nnandrew/heartbreak/CONCEPTS/backPCB.png

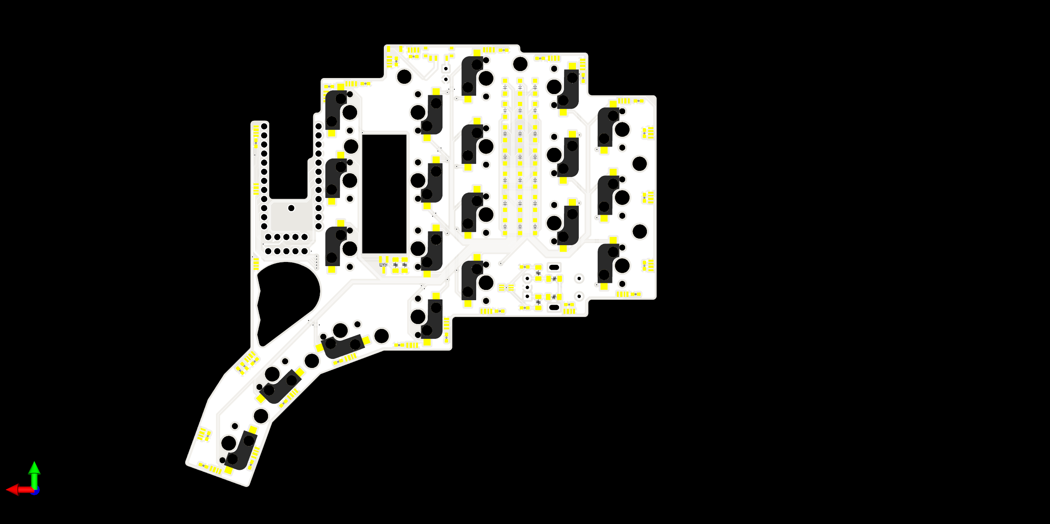
CONCEPTS/backPCB.png
