nnandrew/heartbreak/CONCEPTS/centerGlow.png

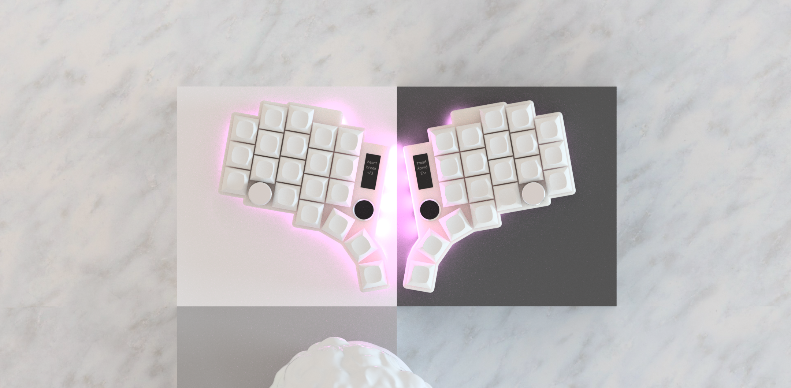
CONCEPTS/centerGlow.png
