nnandrew/heartbreak/CONCEPTS/david.png

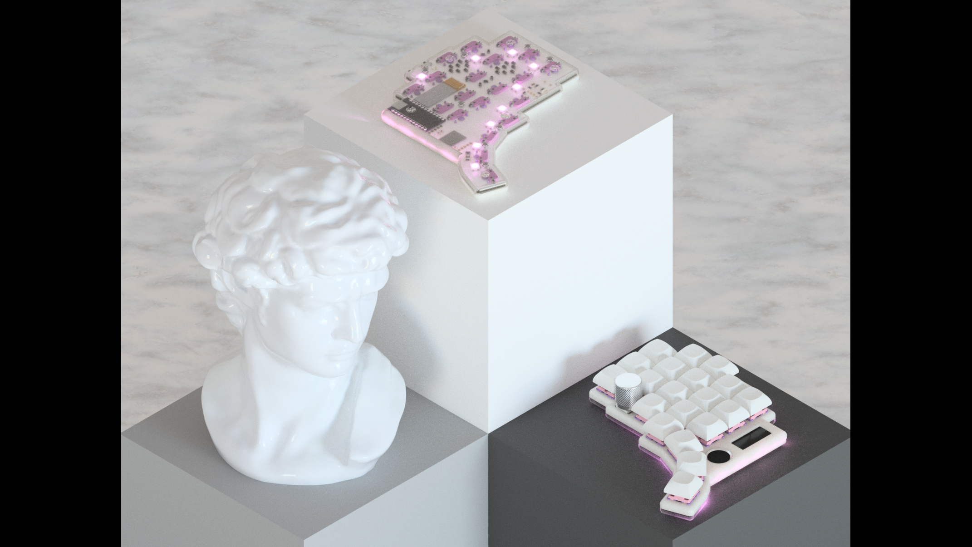
CONCEPTS/david.png
