nnandrew/heartbreak/CONCEPTS/davidraw.png

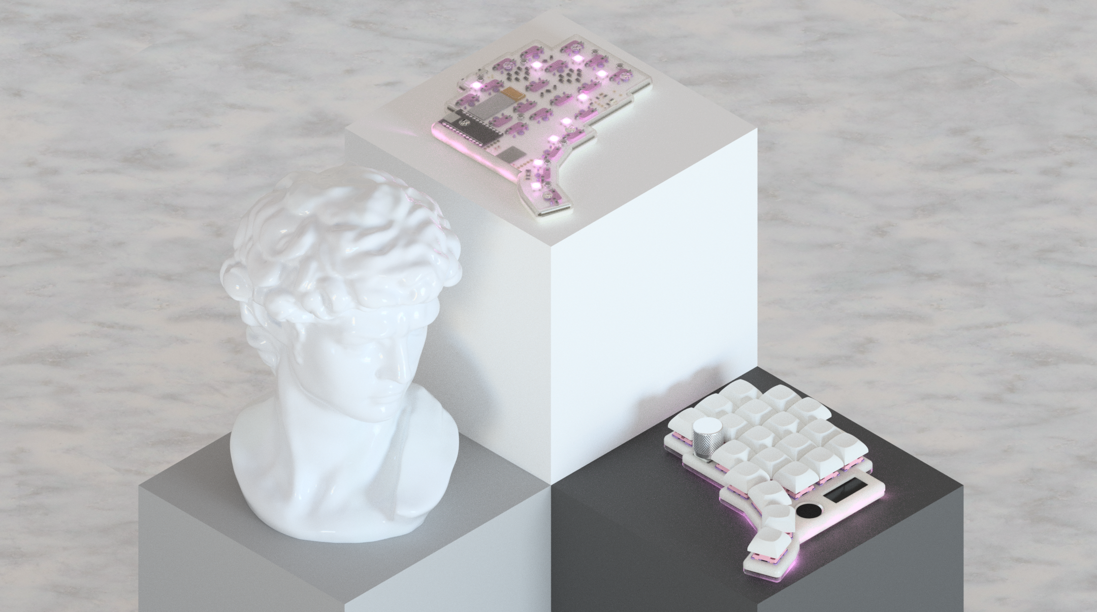
CONCEPTS/davidraw.png
