nnandrew/heartbreak/CONCEPTS/heartbreak1.png

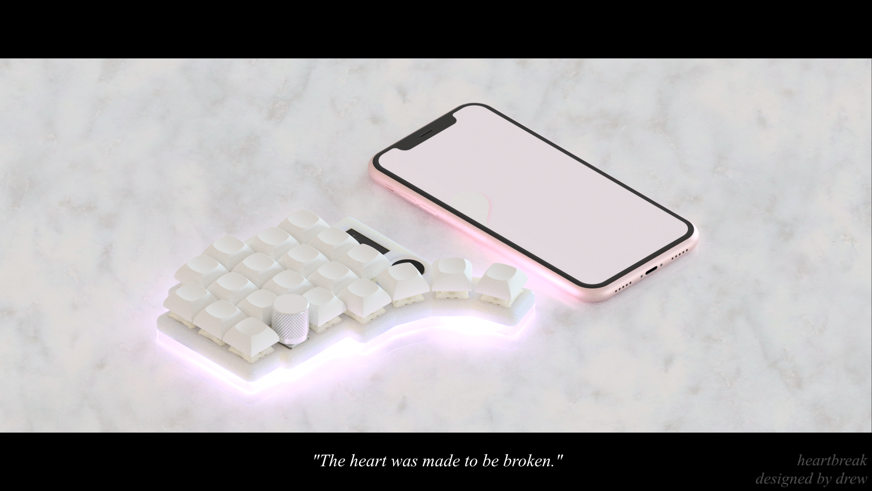
CONCEPTS/heartbreak1.png
