nnandrew/heartbreak/CONCEPTS/heartbreak2.png

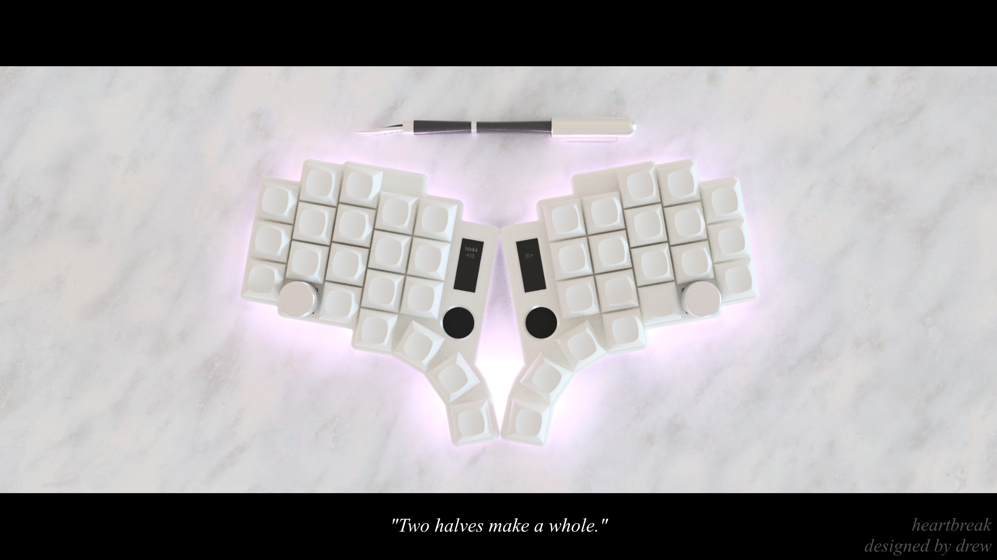
CONCEPTS/heartbreak2.png
