nnandrew/heartbreak/CONCEPTS/keeb.png

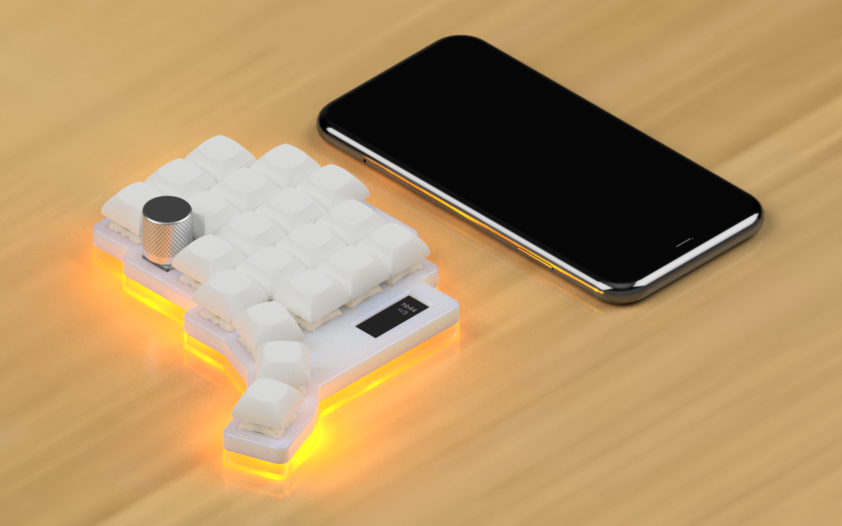
CONCEPTS/keeb.png
