nnandrew/heartbreak/CONCEPTS/scale_render.jpg

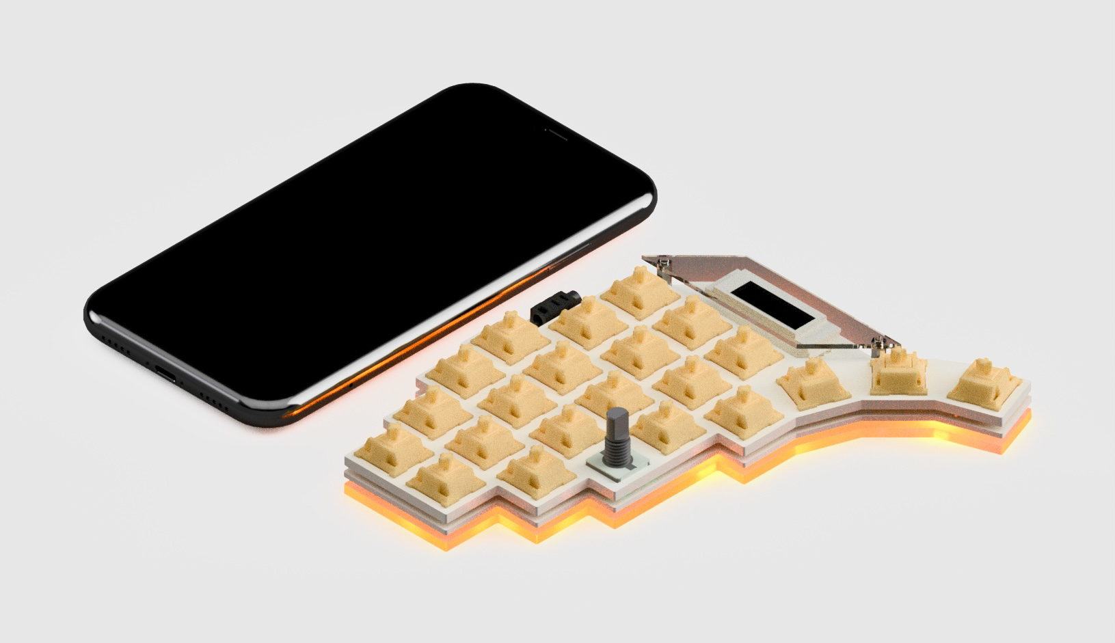
CONCEPTS/scale_render.jpg
