nnandrew/heartbreak/CONCEPTS/switches_render.jpg

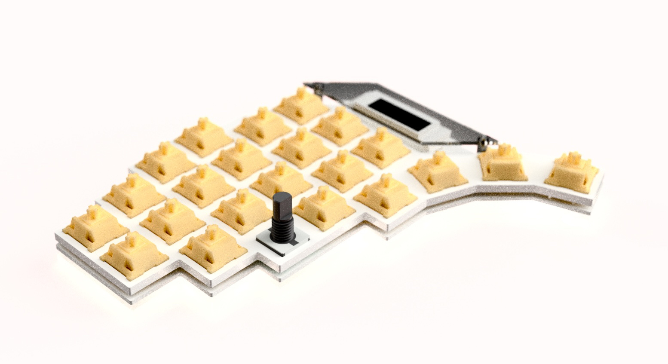
CONCEPTS/switches_render.jpg
