nnandrew/heartbreak/CONCEPTS/under.png

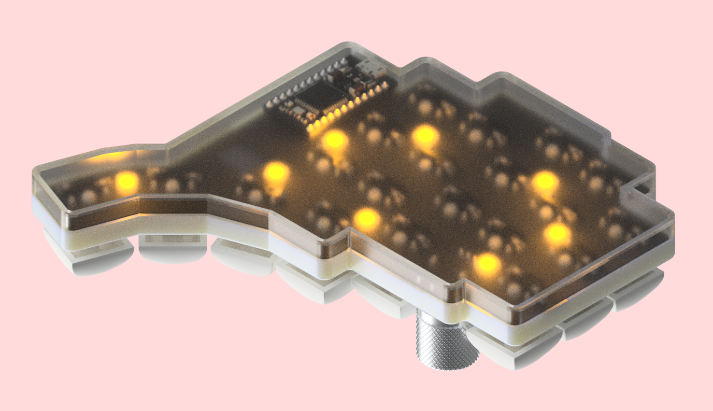
CONCEPTS/under.png
