nnandrew/heartbreak/3D/nice!view.step

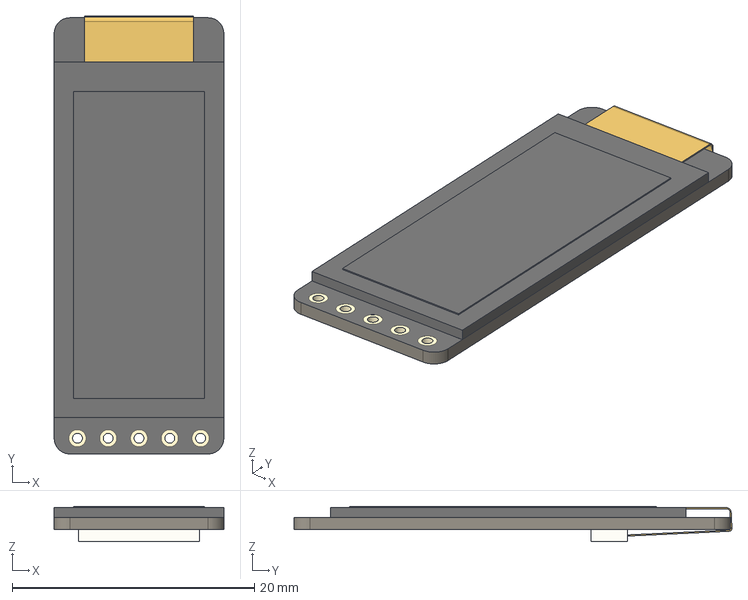
[picture p31: CAD file, 2022-10-16]
3D/nice!view.step
14.0 x 36.1 x 2.90 mm
