nnandrew/heartbreak/3D/DSA_1u.step

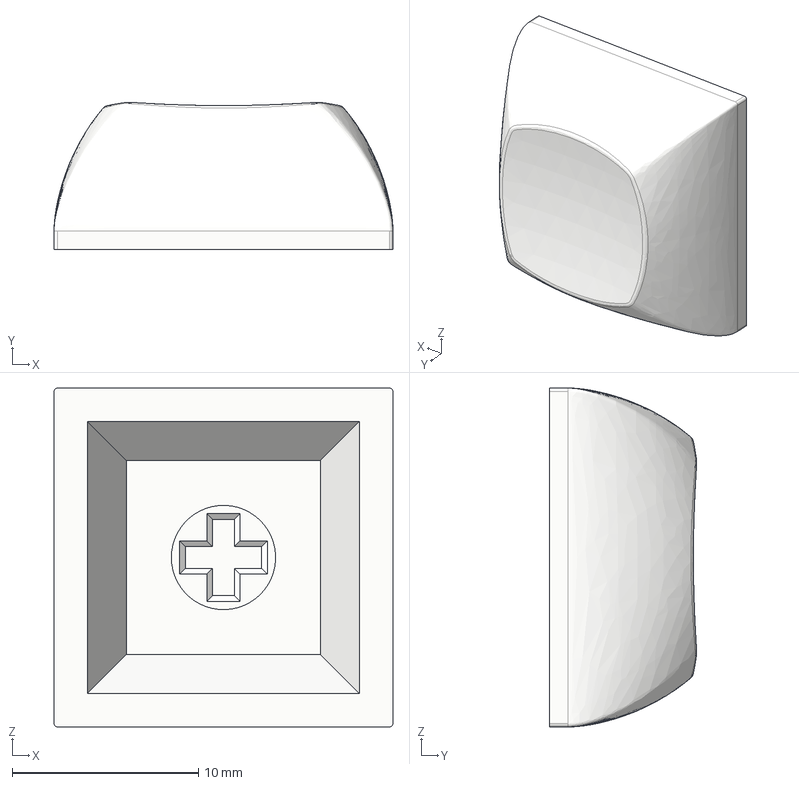
[picture p32: CAD file, 2022-10-16]
3D/DSA_1u.step
18.2 x 7.91 x 18.2 mm
