nnandrew/heartbreak/3D/CherryMX-Switch.step

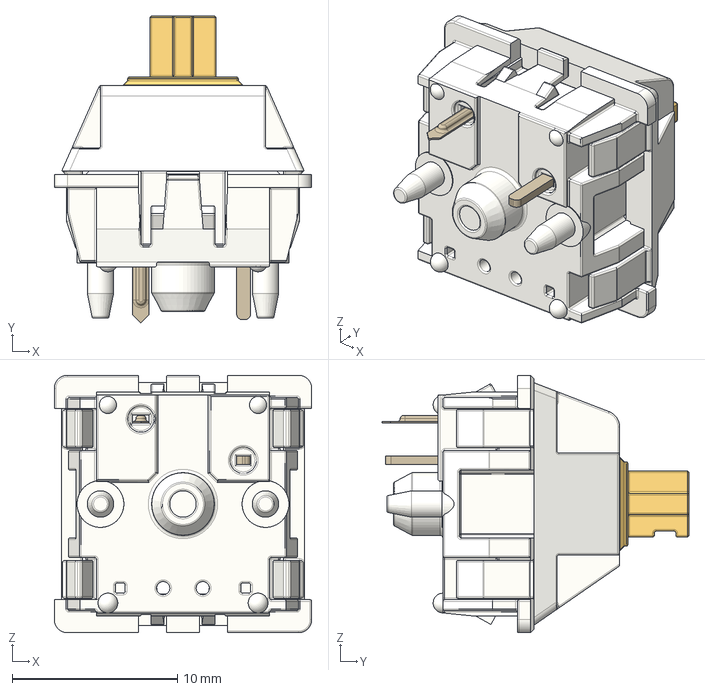
[picture p33: CAD file, 2022-10-16]
3D/CherryMX-Switch.step
15.6 x 18.6 x 15.6 mm
