nnandrew/heartbreak/3D/ec11.STEP

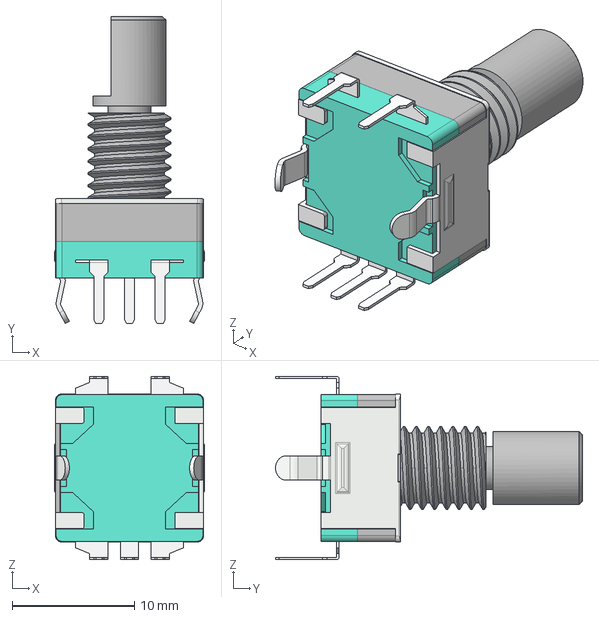
[picture p34: CAD file, 2022-10-16]
3D/ec11.STEP
12.3 x 25.1 x 15.0 mm
